ArthurBondar/Turtle/Line Camera/Software_RPI/gps_class.py

#!/usr/bin/python2


'''
    Changed: October 7, 2018

    Class to use read and record GPS data
    Spawns a thread to capture data over UART
    Saves data in a CSV format

    Updated: February 23, 2019
    Removed file creation on boot
    Only creates a file when Fix is established

'''

import os
from gps import *
from time import *
import time
import threading
import csv

gpsd = None
gpsp = None

# Class to run thread for GPSD
class GpsPoller(threading.Thread):

  def __init__(self):
    threading.Thread.__init__(self)
    global gpsd #bring it in scope
    gpsd = gps(mode=WATCH_ENABLE) #starting the stream of info
    self.current_value = None
    self.running = True #setting the thread running to true

  def run(self):
    global gpsd
    while gpsp.running:
      gpsd.next() #this will continue to loop and grab EACH set of gpsd info to clear the buffer

# Class to interract with the gps and save CSV
class GPS_class():
  gpsp = None                          # Thread to read form gpsd
  fname = ""                           # CSV file name

  # function that check existence of a file
  def FileNamer(self, file, ext):
    # check if file doest exist already
    tmp = """{path}.{extension}""".format(path=file, extension=ext)
    if not os.path.isfile(tmp):
      return tmp
    # make new file name with index 1-100
    for i in range(1,100):
      tmp = """{path}_{num}.{extension}""".format(path=file, num=i, extension=ext)
      if not os.path.isfile(tmp):
          return tmp
    return None

  # init function, starts gps thread
  def __init__(self, usb_path):
    global gpsp
    gpsp = GpsPoller()             # create the thread
    gpsp.start()                   # start it up
    #self.setTime()                # set system time
    # generate filename for CSV
    self.fname = self.FileNamer(usb_path + time.strftime("%d_%m_%Y"), "csv")

  # function to write one row of data into CSV, only when fix is detected
  def writeCSV(self):

    # Saving data when GPS fix is established
    if(gpsd.fix.mode > 1):
      # Writing CSV Header
      if not os.path.isfile(self.fname):
        with open(self.fname, "wb") as fdata:
          writer = csv.writer(fdata, delimiter=',', quotechar='"', quoting=csv.QUOTE_NONE)
          writer.writerow(('Fix mode','Time','Speed','Longitude','Latitude','Climb', 'Altitude','Track'))

      # Wiriting CSV Data
      with open(self.fname, "a") as fdata:
        # Writing CSV data
        row = []
        row.append(str(gpsd.fix.mode))
        row.append(str(gpsd.utc))
        row.append(str(gpsd.fix.speed))
        row.append(str(gpsd.fix.longitude))
        row.append(str(gpsd.fix.latitude))
        row.append(str(gpsd.fix.climb))
        row.append(str(gpsd.fix.altitude))
        row.append(str(gpsd.fix.track))
        # Write to CSV file
        writer = csv.writer(fdata, delimiter=',', quotechar='"', quoting=csv.QUOTE_NONE)
        writer.writerow(row)
        return str(row)

    else:
      return "no sat fix"

  # debug function to dump gps data to the screen
  def dumpData(self):
    if hasattr(gpsd.fix, 'mode'):  print "mode:", gpsd.fix.mode
    if hasattr(gpsd.fix, 'time'):  print "time:", gpsd.fix.time
    if hasattr(gpsd.fix, 'speed'): print "speed:", gpsd.fix.speed #* gps.MPS_TO_KPH
    if hasattr(gpsd.fix, 'lon'):   print "longitute:", gpsd.fix.longitude
    if hasattr(gpsd.fix, 'lat'):   print "latitude:", gpsd.fix.latitude
    if hasattr(gpsd.fix, 'climb'): print "climb:", gpsd.fix.climb
    if hasattr(gpsd.fix, 'alt'):   print "altitude:", gpsd.fix.altitude
    if hasattr(gpsd.fix, 'track'): print "track:", gpsd.fix.track
    print " "

  # get time from GPS and set system time
  def setTime(self):
    time.sleep(5)            # wait for gps to read date properly
    os.system('sudo date +%Y%m%d%T -s \"{}\" --utc'.format(gpsd.utc))

  # closing threads
  def close(self):
    gpsp.running = False
    print("GPS Class: closing")
    gpsp.join()               # wait for the thread to finish what it's doing


# When class module is started by itself
# Following code is used for testing the LED's
if __name__ == "__main__":

  OUT_FILE = "/home/pi/"

  try:
    print("Starting GPS debugging session")
    gps = GPS_class(OUT_FILE)
    # gps.setTime()
    # print data in 10 rows
    for i in range(0, 10):
      print gps.writeCSV()
      time.sleep(1)
    # close GPS
    gps.close()
    print("Finished debugging session")
    print("Output file is: "+gps.fname)

  except: pass
